gruvw/2d_plotter/2d_plotter/src/hardware/buzzer.h

#pragma once

// Plays the start sound on the buzzer
void play_start_sound();

// Plays the ready sound on the buzzer
void play_ready_sound();

// Plays the done sound on the buzzer
void play_done_sound();
